nakujaproject/internship2022/Propulsion/Week 13/week 13 progress report.pdf

NAKUJA INTERNSHIP

## WEEK 13 PROGRESS REPORT

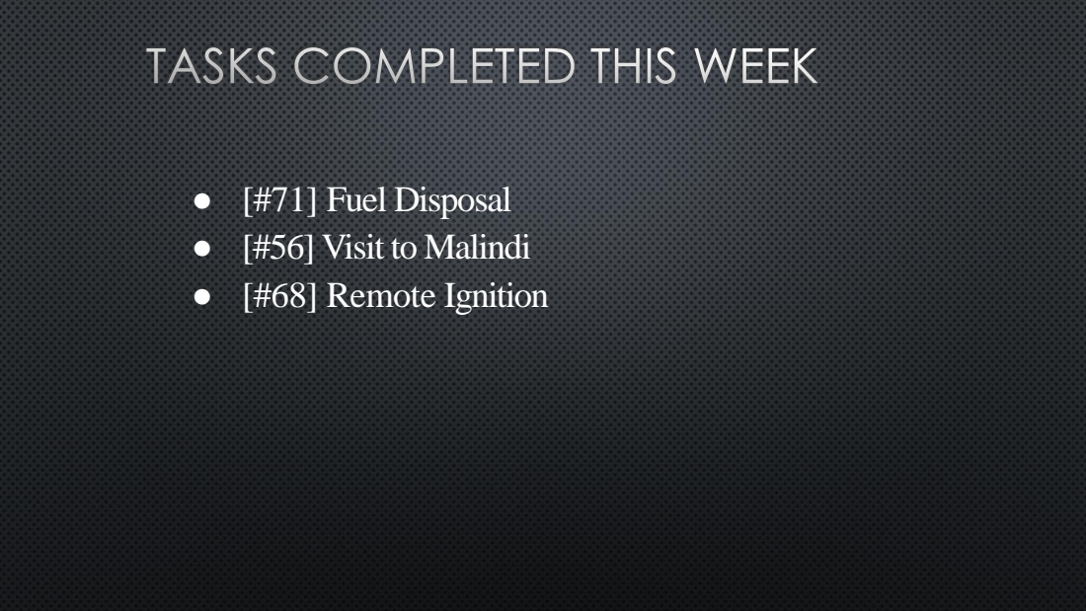
[picture p85: page 2]

● [#71] Fuel Disposal
● [#56] Visit to Malindi
● [#68] Remote Ignition

# # Safe Fuel Disposal

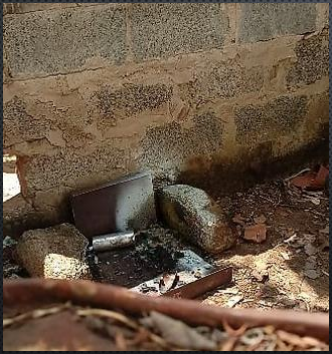
[picture p86: figure]

## The two grains of fuel

## casted on Monday had

stuck | to | the | casing

requiring safe disposal.

# # Trip to Malindi

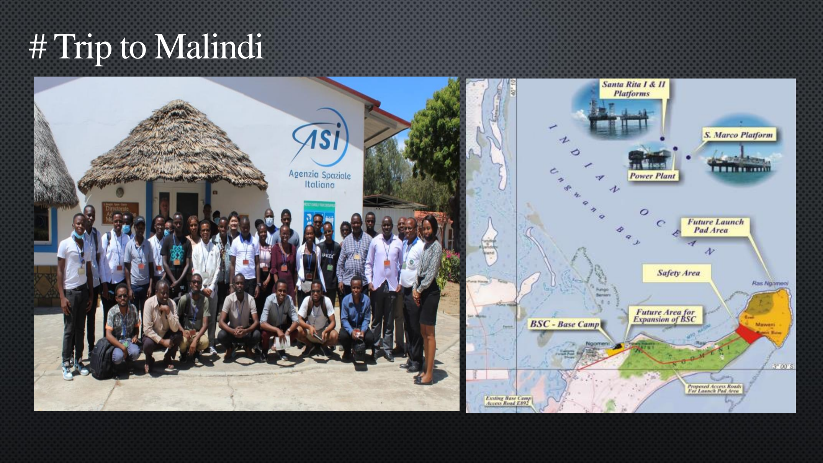
[picture p87: page 4]

## We will be using ESP32 LOLIN module to switch relay via

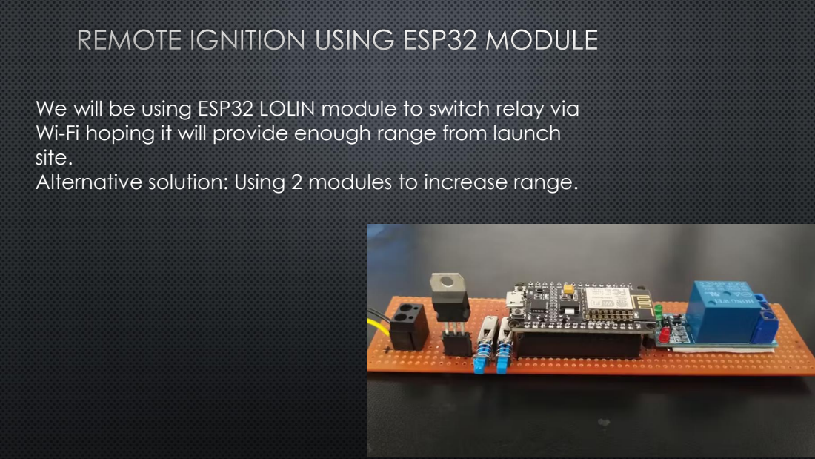
[picture p88: page 5]

Wi-Fi hoping it will provide enough range from launch
site.
Alternative solution: Using 2 modules to increase range.

TASKS THIS WEEK

## - [#108] Remote Ignition - [#36] Snap Ring Purchase - [#56] Fuel Casting for Test Flight - [#150] Test Flight

Month; Intern week; Tasks; Jan; Feb; Week 4; Fabrication of items & Fuel casting

Week 1 | Designs [Fuel, Casing, Nozzle, Bulkhead, Casting tools, Teststand]

Week 2 | Fabrication of items

Week 3 | Fuel Fabrication and test stand revamp

Week 5 | Iterative Fuel tests

Week 6 | Launch Pad design and iterative fuel tests

Week 7 | Iterative fuel testing and improvement
