nakujaproject/internship2022/Airframe/Week12/Airframeprogressreport_04_09_week.pdf

# Introduction of internship

### January 2022

Tasks done

- Fabricated the new airframe for test launch
- Tested the nichrome wire for ejection charge
- Secure skeleton for assembling the subsystems

Tasks to be done

- Nose cone adjustments and printing
- Fins fabrication
- Start assembling the skeleton ready for Friday test launch
- Print launch lug

Timeplan

April 18th - 23rd | - Test launch
| - Fabricate duplicate body tubes
April 25th - 30th | Possible launch
May 2nd - 7th | Possible launch
