nakujaproject/internship2022/Propulsion/week 11/week 11 progress report.pdf

NAKUJA INTERNSHIP

## WEEK 11 PROGRESS REPORT

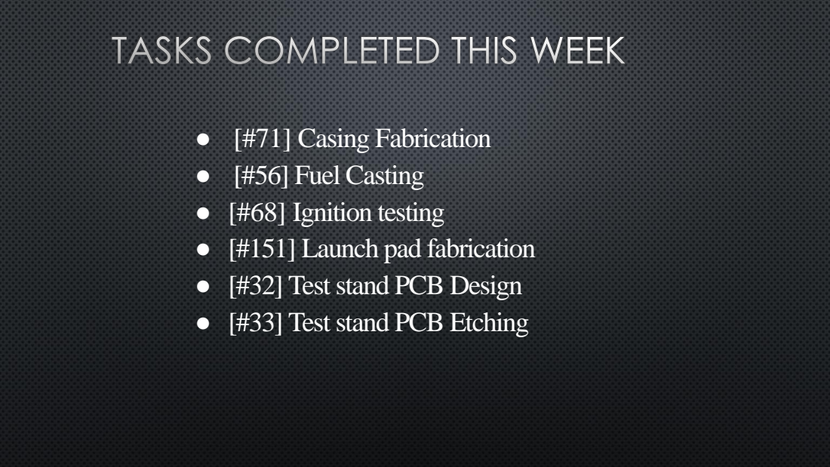
[picture p94: page 2]

● [#71] Casing Fabrication
● [#56] Fuel Casting
● [#68] Ignition testing
● [#151] Launch pad fabrication
● [#32] Teststand PCB Design
● [#33] Test stand PCB Etching

# #71 Casing fabrication

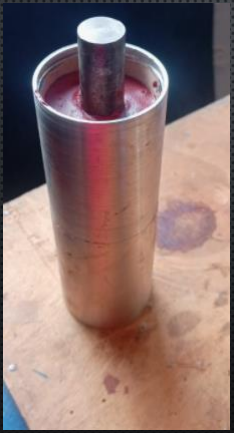
[picture p95: figure]

We | fabricated | another

## casing to be used for the

test launch on Thursday.

# Fuel Casting

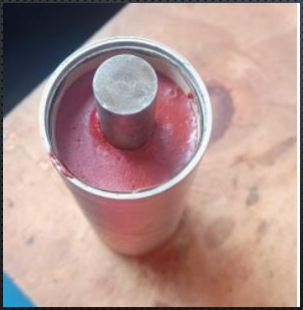
[picture p96: figure]

We prepared a single grain of fuel.

## The mixing ratio was 67:33

## potassium nitrate to sorbitol, 5g of

## iron oxide. Fuel was cast directly to

## casing. The single grain will be used

forthe testlaunch tomorrow.

# LAUNCH PAD FABRICATION

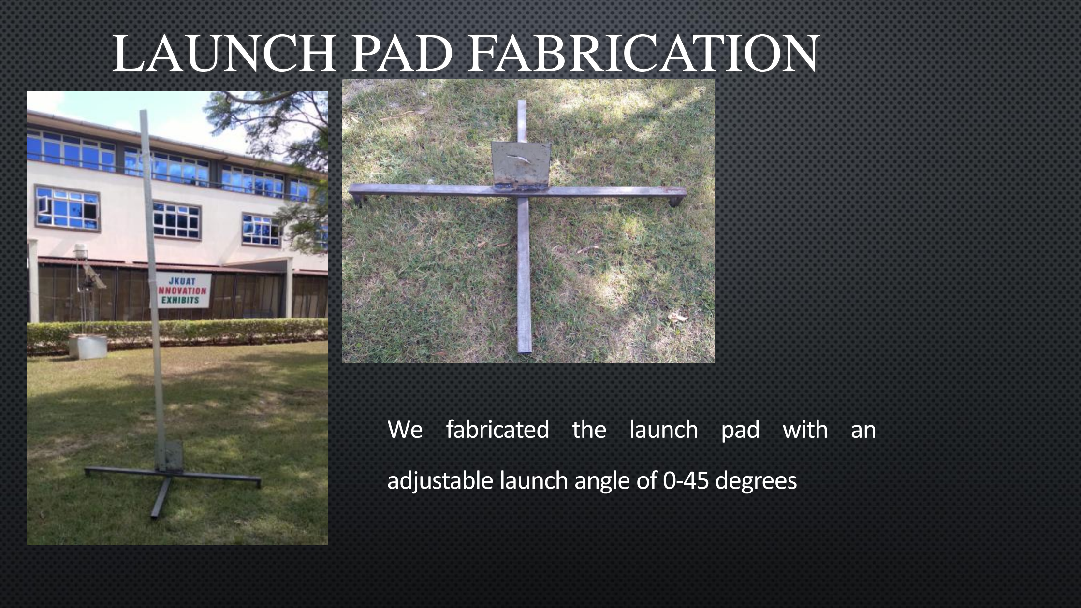
[picture p97: page 5]

## We fabricated the launch pad with an

## adjustable launch angle of 0-45 degrees

# Etched Test Stand PCB

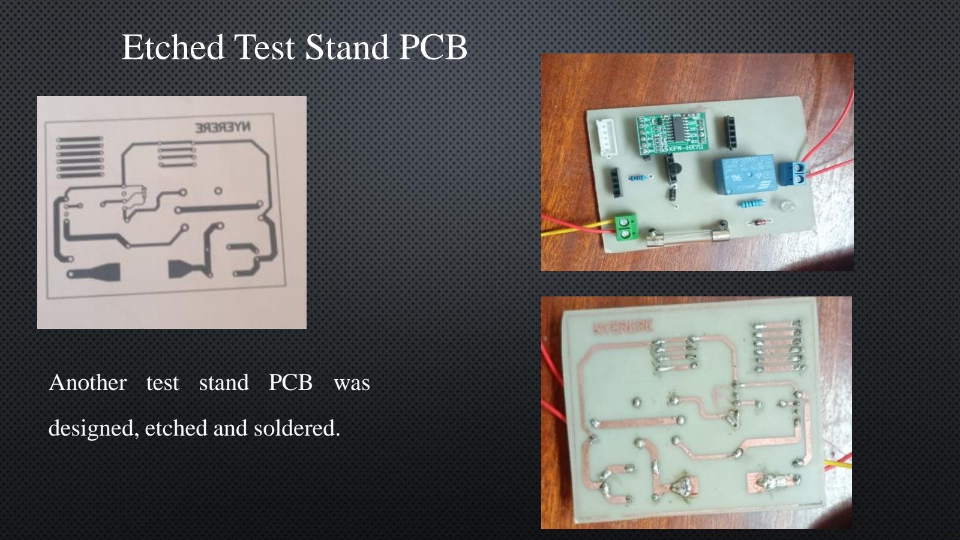
[picture p98: page 6]

### Another test stand PCB was

designed, etched and soldered.

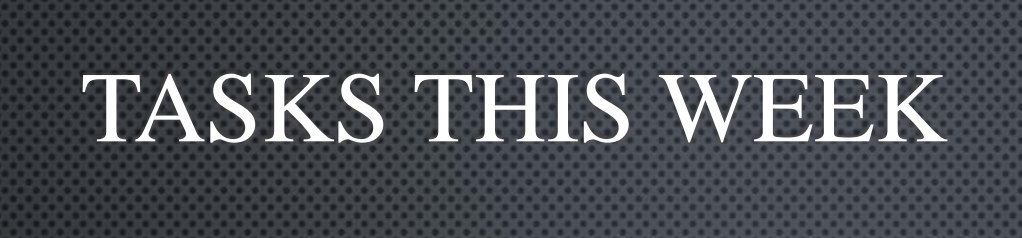
[picture p99: figure]
TASKS THIS WEEK

### - [#150] Test Flight

Month; Intern week; Tasks; Jan; Feb; Week 4; Fabrication of items & Fuel casting

Week 1 | Designs [Fuel, Casing, Nozzle, Bulkhead, Casting tools, Teststand]

Week 2 | Fabrication of items

Week 3 | Fuel Fabrication and test stand revamp

Week 5 | Iterative Fuel tests

Week 6 | Launch Pad design and iterative fuel tests

Week 7 | Iterative fuel testing and improvement
