nakujaproject/internship2022/avionics/Week6/Avionics Progress Report Week6 updated.pdf

# Nakuja Project

Week 6 Progress Report
Edwin Mwiti
Junn Hope

# Tasks this week

- [#] : Test Payload
- [#Issue 83] : Power Management
- Flight computer programming and documentation

# [#] : Test Payload

- We performed payload tests on Friday,25th Feb.
- Signal strength was also severely affected as we got RSSI values as low as -88, which was below our estimated range of -50 to -70
- The test brought to light factors we had not looked into:
- 1) Electromagnetic interference –The data received from the sensors gave negative result, a result of the interference. The drone rotors motion caused an electromagnetic field which affected the sensors operation-particularly the BMP 180.
- 2) signal interference – the RF signals from the drone interefered with the RF signals within our Wi-Fi network.

# [#] : Test Payload

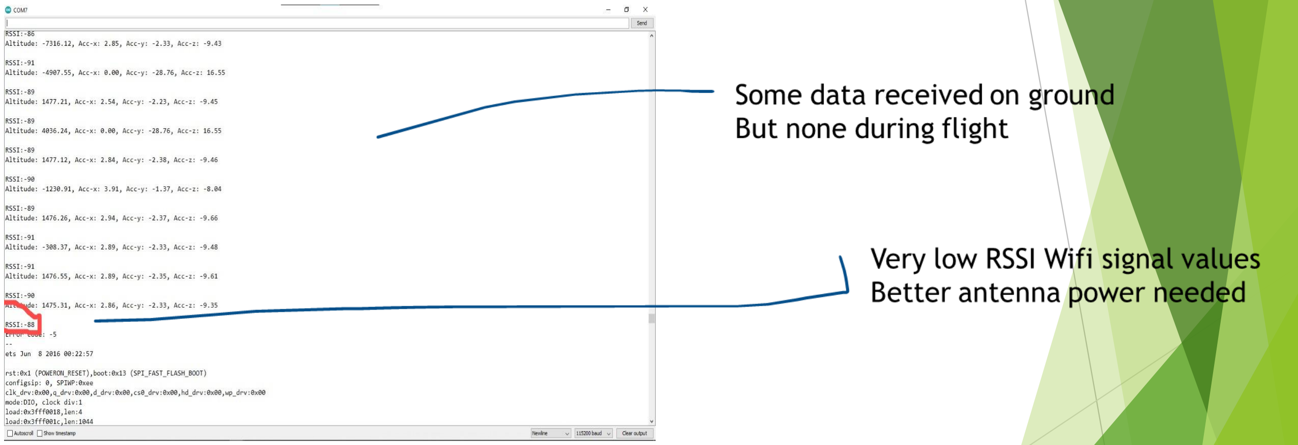
[picture p161: figure]

## Flight computer programming and documentation

- Ongoing programming of flight computer
- Restructuring code as a state machine
- Every interval is a state. E.g
- This will help in scaling the software for future versions
- Observation: need to have a means of restarting the flight computer remotely

# [#Issue 83] : Power Management

- The design of the power distribution board is done and is currently under review

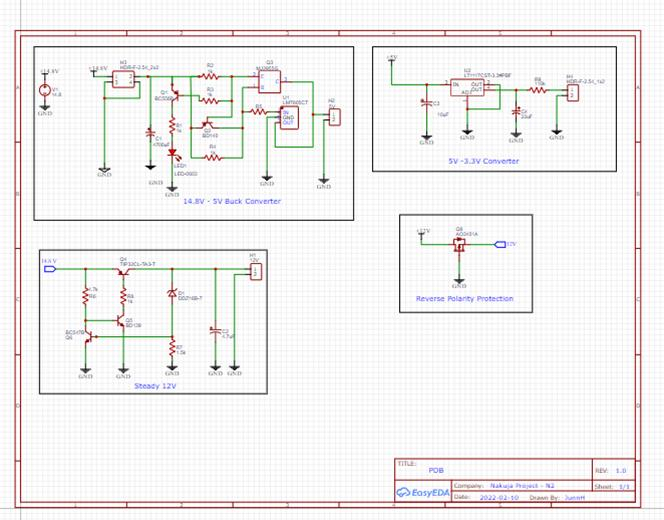
[picture p162: figure]

# Tasks this week

- [#Issue 26] : Improve on Kalman filter performance
- [#Issue 103] : Build Wi-Fi Amplifier
- [#Issue 34] : Programming the Flight Computer
- [#Issue 18] : Launch pad design
