nakujaproject/internship2022/Propulsion/Week 5 (10th - 16th)/Valerian Nyerere Progress Report.pdf

# Internship 2022

# Progress report format for team meeting

Name: NYERERE VALERIAN
09/02/2/2022 - 15/02/2022

## Tasks completed last week

- [#56] Fuel fabrication (Wednesday)
- [#71] Casing fabrication (Thursday)
- [#72] Crimson powder development.(Friday)
- [#32] Design of the Test-Stand PCB redo (Monday)
- [#88] Crimson powder ejection test. (Tuesday)

## Fuel Fabrication

We had to fabricate more fuel following the right procedure and ratio.

We used 65% potassium nitrate and 35% sorbitol.

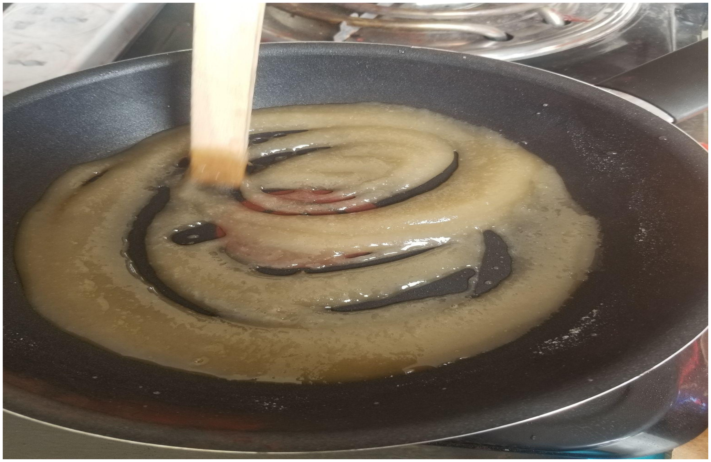
[picture p163: figure]

## Crimson powder test

Tested the crimson powder explosion rate.

Found out the more dry it is, the more efficient it works.

## Crimson powder development

Developed more crimson powder taking into consideration the observations made in the first ejection test.

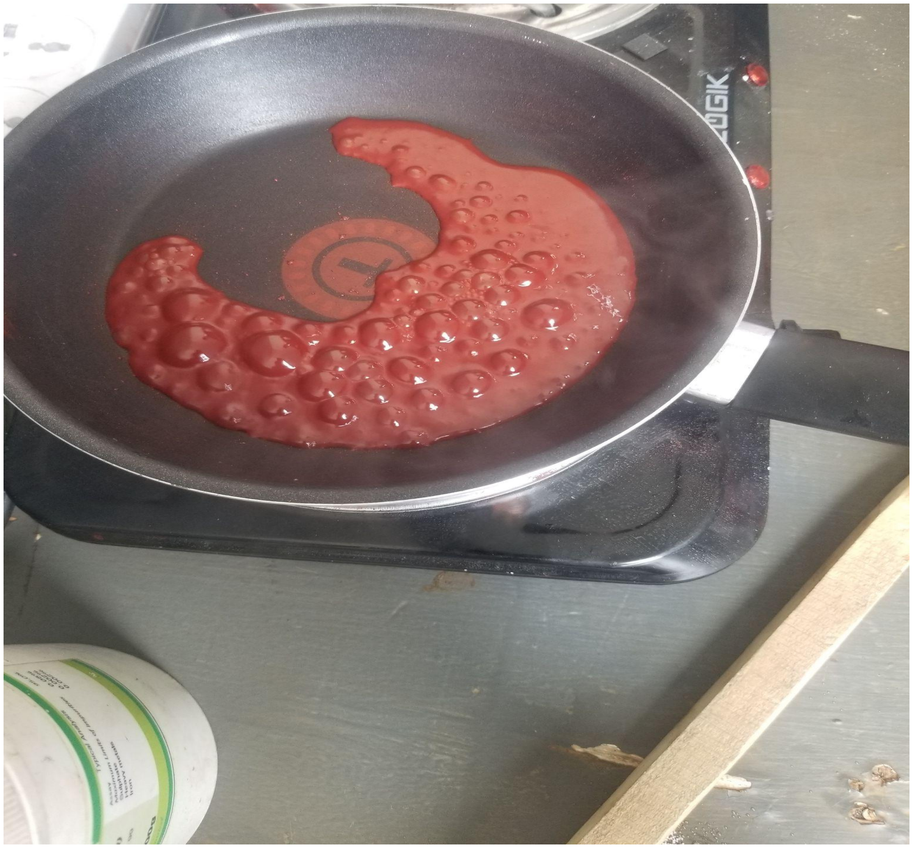
[picture p164: figure]

## Design of the Test-stand PCB

Redesigned the Test-stand PCB.

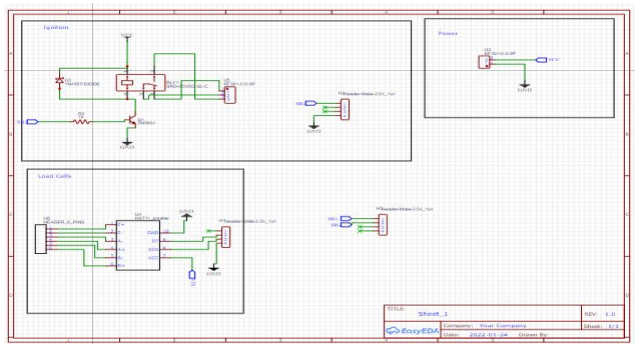
[picture p165: figure]

Still in progress.

## Tasks in this week

- [#85] Preparation of potassium perchlorate.
- [#33] Test stand PCB etching.
- [#19] Static firing tests.

## Timeline

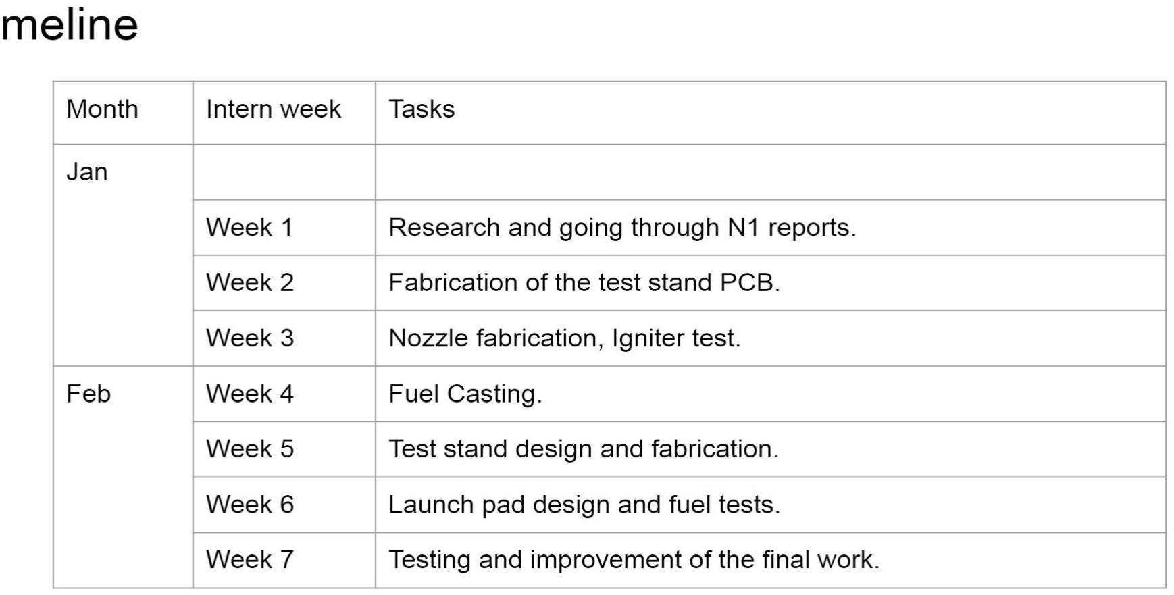
[picture p166: page 8]

Month | Intern week | Tasks

Jan

Week 1

Week 2

Week 3

Feb | Week 4

Week 5

Week 6

Week 7
