nakujaproject/internship2022/Propulsion/Week 6 (17th - 23rd)/Valerian Progress Report.pdf

## Internship 2022

## Progress report format for team meeting

Name: NYERERE VALERIAN KWAMBOKA 16/02/2022- 22/02/2022

Tasks completed last week

- [#32] Test stand PCB design
- [#33] PCB Etching.
- [#68] Ignition Testing.
- [#19] Iterative static firing test. (First)

PCB DESIGN AND ETCHING(Failed)

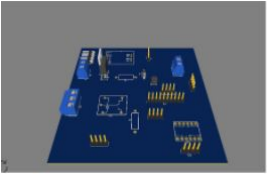
[picture p167: figure]

The first three designs failed. This is the current design that is being etched at the moment.

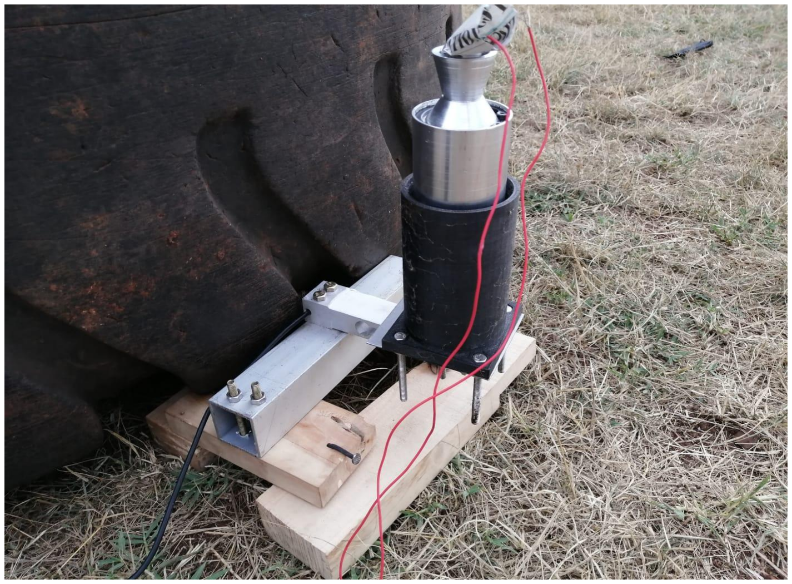
[picture p168: figure]

STATIC FIRING

The setup of the test stand.

STATIC TEST FIRING VIDEO

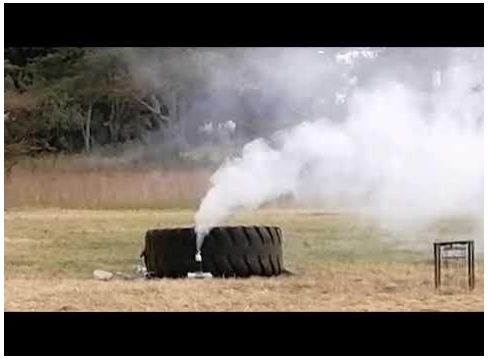
[picture p169: figure]

OBSERVATIONS.

- The igniter took a few seconds before igniting opposed to the immediate response we expected. That was after several tries.
- The fuel took close to one minute before it fully burnt out. According to the simulations, the fuel should take 2 seconds to burn out.
- No data was collected from the Raspberry Pi.

Tasks in this week

- [#85] Preparation of Potassium Perchlorate.
- [#56] Fuel casting.
- [#32] Test stand PCB design
- [#33] PCB Etching.
- [#68] Preparation and Ignition Testing.
- [#71] Casing fabrication (Finalising).

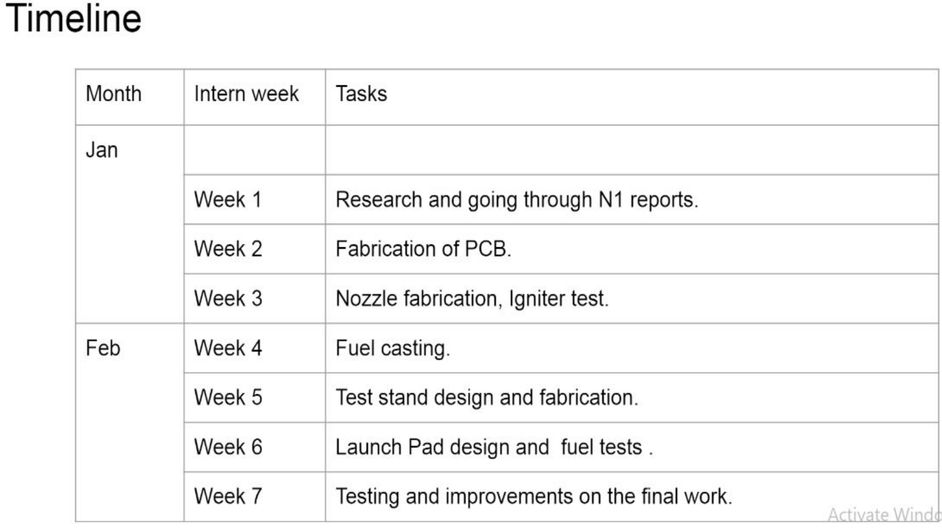
[picture p170: page 8]

Timeline

Month | Intern week | Tasks

Jan

Week 1

Week 2

Week 3

Feb | Week 4

Week 5

Week 6

Week 7
