nakujaproject/internship2022/Propulsion/Week 4 (3rd - 9th)/Valerian Nyerere. Progress Report.pdf

# Internship 2022

# Progress report format for team meeting

## Name: NYERERE VALERIAN

02/02/2022 - 09/02/2022

# Tasks completed last week

## - [#56] Fuel casting (Wednesday) - [#22] Static fire safety orientation (Thursday) - [#11] Casting tool fabrication (Friday) - [#72] Crimson powder development (Monday - Tuesday)

# Fuel casting

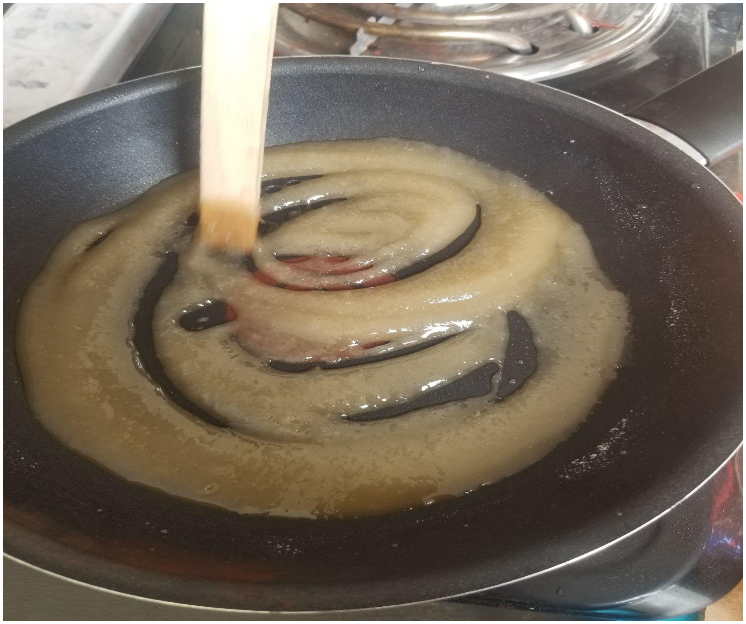
[picture p234: figure]

Heating a mixture of potassium nitrate and sorbitol to make the fuel. In the ratio 65: 35
respectively.

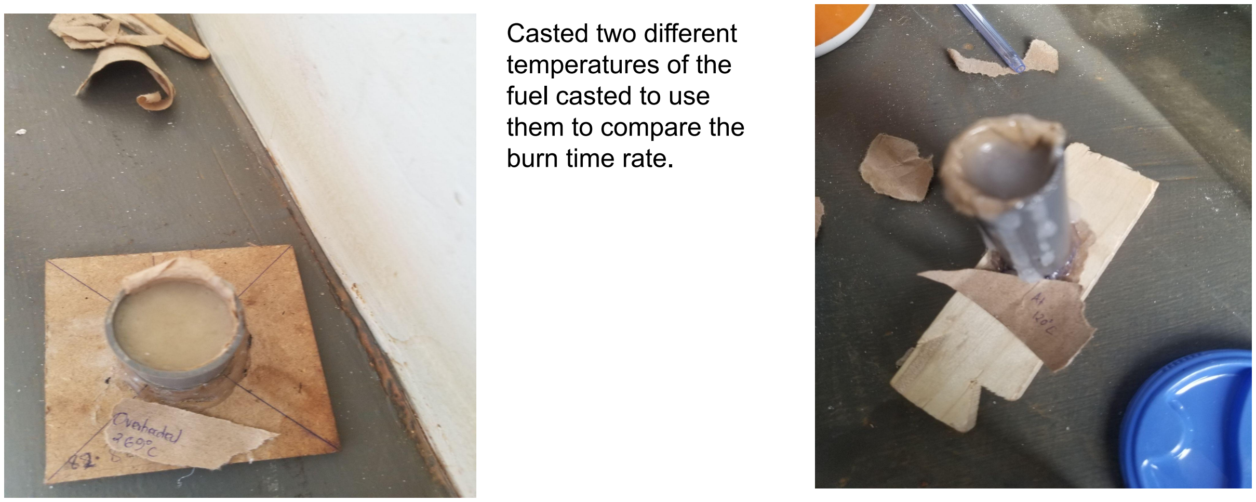
[picture p235: page 4]

Casted two different
temperatures of the
fuel casted to use
them to compare the
burn time rate.

# Casting tools fabrication

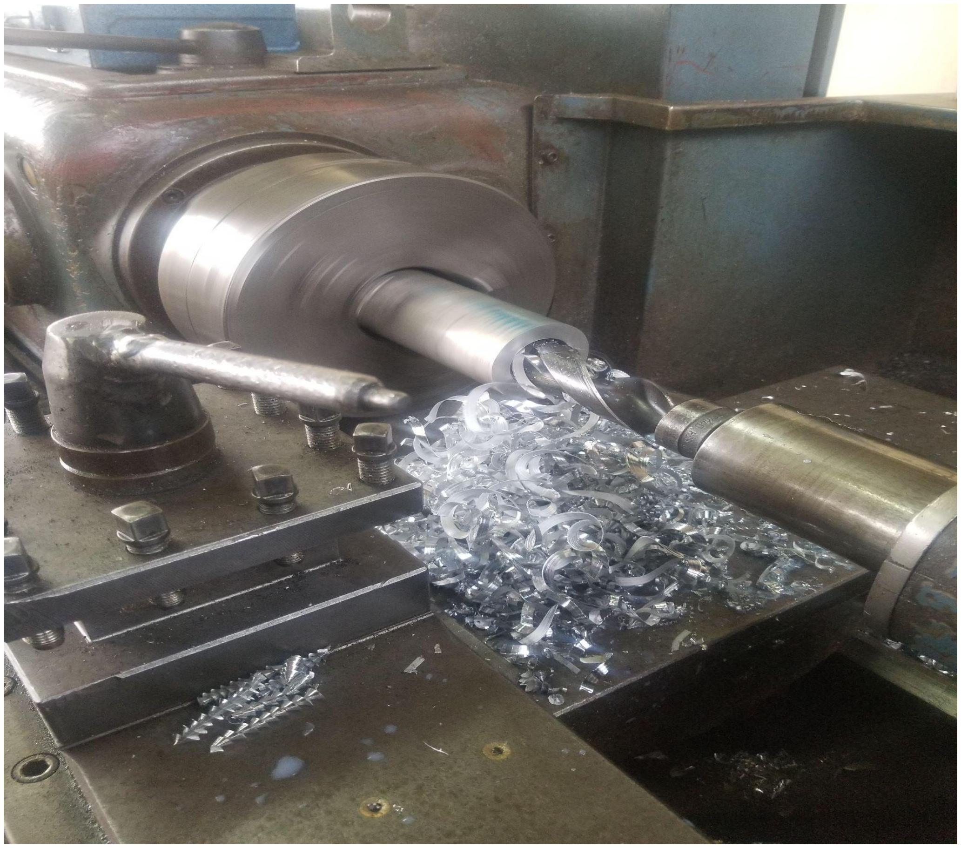
[picture p236: figure]

# Crimson Powder Development

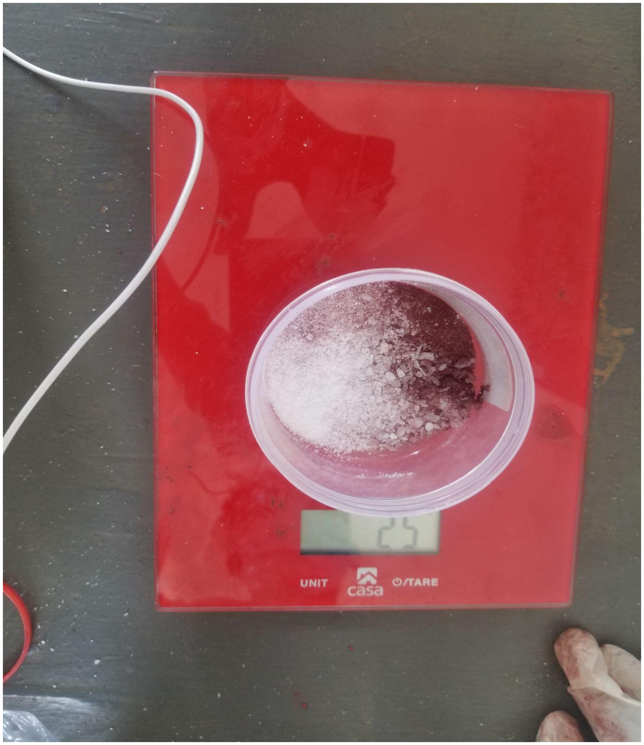
[picture p237: figure]

A mixture of potassium nitrate, iron oxide and ascorbic acid to make the ejector.

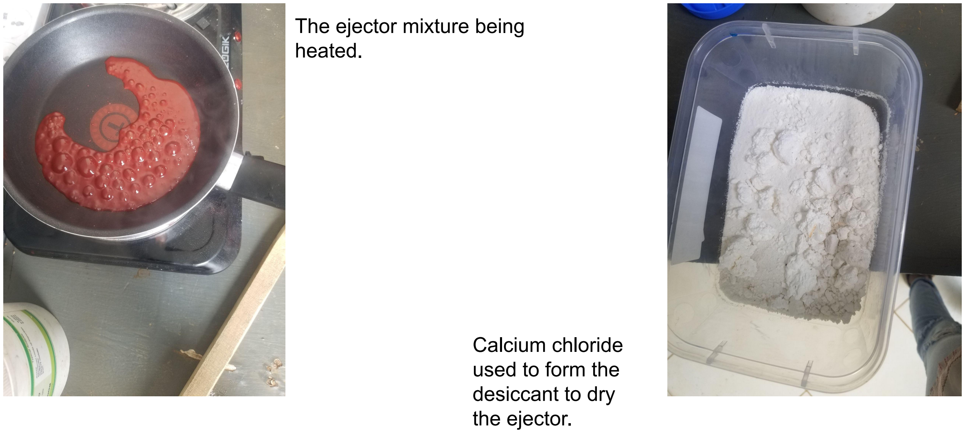
[picture p238: page 7]

The ejector mixture being
heated.

Calcium chloride
used to form the
desiccant to dry
the ejector.

# Tasks in this week

## - [#69] KNPSB Trials - [#71] Casing fabrication - [#56] Fuel fabrication - #73] KNSB Burn time tests

# Timeline

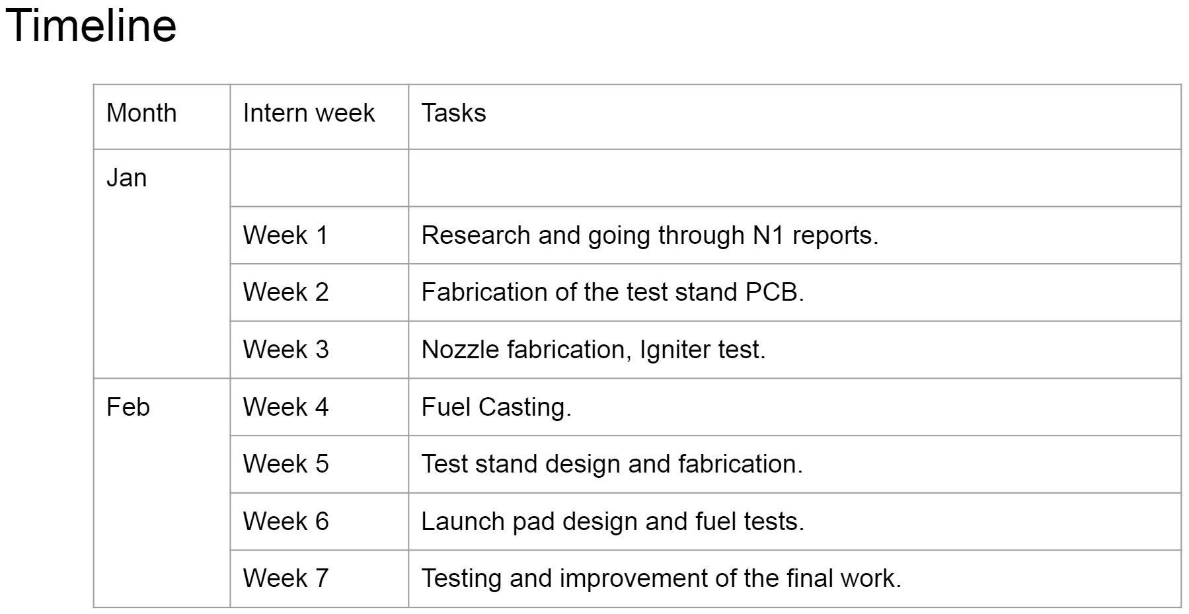
[picture p239: page 9]

Month | Intern week | Tasks

Jan

Week 1

Week 2

Week 3

Feb | Week 4

Week 5

Week 6

Week 7
