nakujaproject/internship2022/avionics/Week 1/Nakuja internship Progress report week1.pdf

# Nakuja Internship

# Avionics Progress report

# Edwin Mwiti Junn Hope

# Tasks completed last week

## - [#Issue 4] : Getting acquainted with Avionics and Telemetry resources

## - Onboarding and task planning

## - Flight computer 2 review

# COMMUNICATION CHANNELS

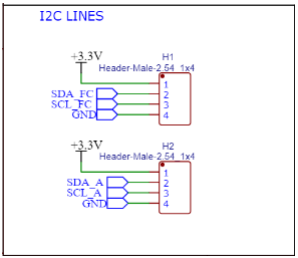
[picture p241: figure]

## - I2C Communication - Avionics board - Flight control board

Flight
control
board

Telemetr
y

Avionics
board

Ground station

Lora/Wifi

i2c

# STORAGE

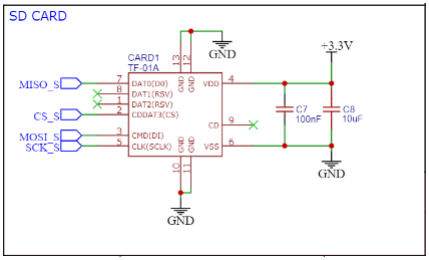
[picture p242: figure]

## - SD CARD MODULE

## Post flight analysis data

## -velocity

## -acceleration

## -gyroscope(orientation)

## -altitude data

# Flight recovery

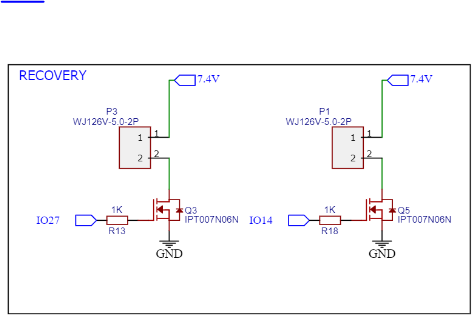
[picture p243: figure]

## Flight recovery system:

## - Parachute deployment

## esp32 ~ 140mA

## mosfet ~ 2A

# Motion Tracking(MPU6050)

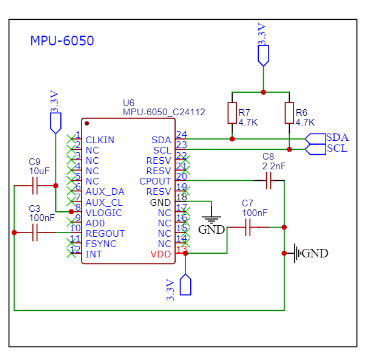
[picture p244: figure]

## - Flight motion tracking:

## Gyroscope

## Accelerometer

# Flight Navigation

## GPS System

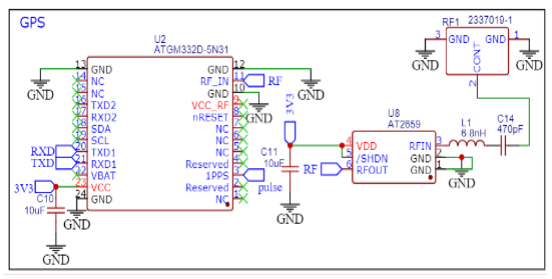
[picture p245: figure]

## - Transmit real-time location data to ground station - For recovery

# Tasks in this week

## - [#Issue 1] : Research on data transmission (lora vs wifi) parameters: 1km > upload speed 272.16 kbps - [#Issue 2] : Research on ground station parameters: 1km > download speed 1000 kbps - [#Issue 3] : Research on ground station dashboard-Grafana - [#Issue 30]: Research on camera module

## Timeline

Month | Intern week | Tasks
| | Getting acquainted with avionics and telemetry resources
| Week 2 | Research on ground station & ground station dashboard Research on camera module Research on Data transmission
| Week 3 | Avionics bay design Launch pad design
| | Improve Kalman filter performance
| Week 5 | Program Avionics and Telemetry boards
| Week 6 | Test the boards
| Week 7 | Testing and launch of N2
Jan | Week 1 | Onboarding
Feb | Week 4 | Research on apogee detection logic
