nakujaproject/internship2022/Flight_Controls/Week 3 (26th - 2nd)/Week3 (upload)progress report.pdf

# Nakuja Internship 2022 Week 3 Progress report format for team meeting

## Name:FLIGHT CONTROL

# Tasks completed last week

- [#29] Soldering of SD card on PCB
- [#24] Design of the reaction wheel

[#29] Soldering of SD card on PCB

Soldering of PCB involved microcontroller pin out identification and connecting the respective pins to the SD card pins

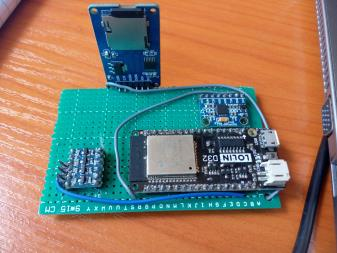
[picture p255: figure]

[#24] Design of the reaction wheel

This was done with the help of simulink(in progress)

# Tasks in this week

- [#24] Design of the reaction wheel(completion)
- [#29] Logging data on SD Card
- [#25]Testing reaction wheel on test bench with current firmware
- [#27]Design mounting case

[#24] Design of the reaction wheel(completion)

This involves design optimization of the CAD model of reaction wheel and fabrication [#29] Logging data on SD Card&[#25]Testing reaction wheel on test bench with current firmware
The two tasks will be done concurrently. The code for this is in progress
[#27]Design mounting case

Onset of the design

## Timeline

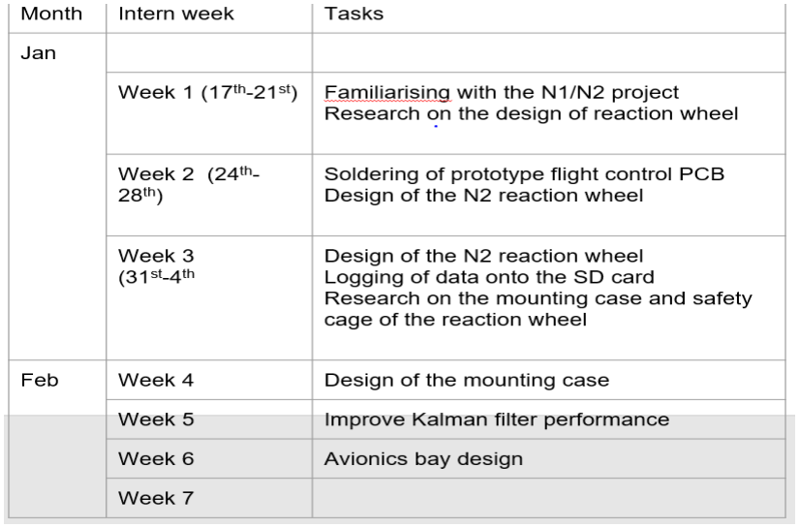
[picture p256: figure]
