nakujaproject/internship2022/Propulsion/Week 3 (26th - 2nd)/Maureen's PROGRESS REPORT.pdf

# Internship 2022

# Wk 3 Progress report

### Name: Gichia Maureen

## Tasks completed last week

[#53]Bulkhead fabrication

[#63]Research on teststand design including use of load cells and the configuration

[#67]Research on N2 motor fuel and work plan development(ongoing)

[#55] Test of new loadcell configuration

[#56] Motor fuel casting1

### [#53]Bulkhead fabrication

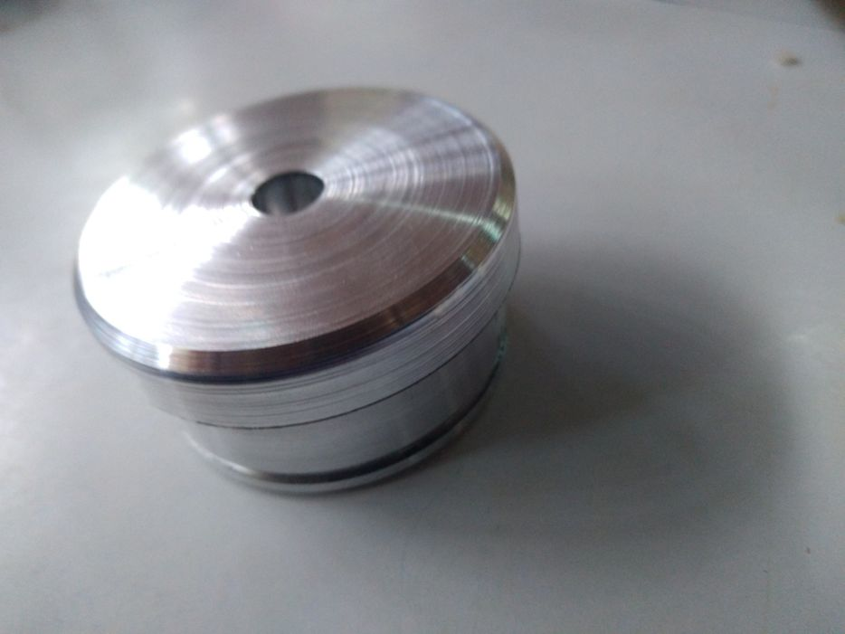
[picture p260: figure]

### [#56] Motor fuel casting1

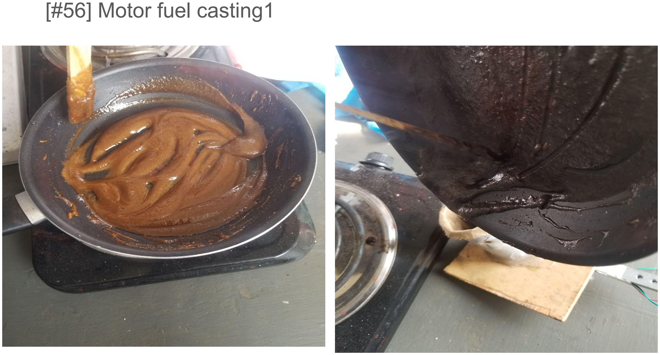
[picture p261: page 4]

## Tasks in this week

●[#52] Nozzle fabrication

- [#21] Research on modification of KNSB fuel
- [#11] Casting tools fabrication
- [#56] Fuel Casting
- [#64] Test stand fabrication
- [#19] Iterative static firing tests
- [#22] Static fire safety orientation

## Timeline

Month | Intern week | Tasks

Jan

Week 1

Week 2

Week 3

Feb | Week 4

Week 5

Week 6

Week 7
