nakujaproject/internship2022/Airframe/Week 1 progress/Airframe.pdf

# Internship 2022

# Progress report format for team meeting

Name: Mark and Vivian

## Tasks completed last week

- [#Github issue number #37]

Describe the completed task with the GitHub issue number

This was the material selection and analysis

## Tasks in this week

- [#Github issue number #38]

This is the design and simulation of the rocket using openrockets.

## Timeline

Month | Intern week | Tasks

Jan

Week 1 | Material selection and analysis
Week 2 | Design and simulation
Week 3 | Fluid dynamics
Feb | Week 4 | Simulation and rocket recovery
Week 5 | Assembly
Week 6 | Assembly
Week 7 | Take-off?
