nakujaproject/internship2022/Propulsion/Week 2(20th - 26th)/Week 2 progress.pdf

# NAKUJA PROJECT INTERNSHIP

# PROGRESS REPORT

# WEEK 2 (20TH JANUARY - 26TH JANUARY)

## Tasks achieved:

## - Purchase of items. - Issue #36

## - Bulkhead design. - Issue #35

## - Casing design. - Issue #6

## - Design and 3D printing of electronics hub. - Issue #16 & 9

## - PCB Design & Etching. - Issue #33 & 32


# 3D PRINTED ELECTRONICS BAY

# TEST STAND PCB


# NOZZLE DESIGN


# NOZZLE FABRICATION


# BULKHEAD DESIGN


# CASING DESIGN


# CASTING TOOLS DESIGN


# MOTOR


# SIMULATION DATA

501 Ns

## Core dia - 17 mm

## Nozzle throat - 12 mm

## Casing thickness - 2 mm

## Design Pressure - 3 Mpa


# Tasks in progress

- Nozzle fabrication.

# - PCB fabrication - (Soldering)

- Design of casting tools.
- Purchase of items.

# Tasks to be done

- Fabrication of Casing and bulkhead.

## - Nozzle fabrication (Finalising)

## - Casting tools fabrication

- Test stand optimization.
- Cast fuel.

# TIMELINE

MONTH | WEEK | ACTIVITY
JAN | 1 | Designs [Casing, Nozzle, Bulkhead, Casting tools, test stand]
| 2 | Fabrication [Casing, Nozzle, Casting tools]
FEB | 3 | Casting of fuel and Test Stand revamp
| 4 | Iterative static firing tests
| 5 | Iterative static fires and fuel improvement
| 6 | Launch Pad design and Fabrication
MAR | 7 | Iterative Static Fires
| 8 | Launch
