nakujaproject/internship2022/Propulsion/Week 1(17th - 19th)/Week 1 progress.pdf

# NAKUJ A PROJECT INTERNSHIP

## PROGRESS REPORT

# WEEK 1 (17 TH JANUARY - 19 TH JANUARY)

Tasks achieved:
- Onboarding and work / tasks planning
- Set up github repository and arrange all relevant info
- Test stand review
- Creation of BOM and first purchase of items.

# Tasks in progress

- Purchase of items
- Bulkhead design
- Design of electronics hub

# Electronics Hub


# Tasks to be done

- 3D printing of electronics hub
- Fabrication of Nozzle, Casing and bulkhead
- Test stand optimization
- Cast fuel
