nakujaproject/internship2022/Flight_Controls/Week 8/NAKUJA PROJECT WEEK 8 PROGRESS REPORT.pdf

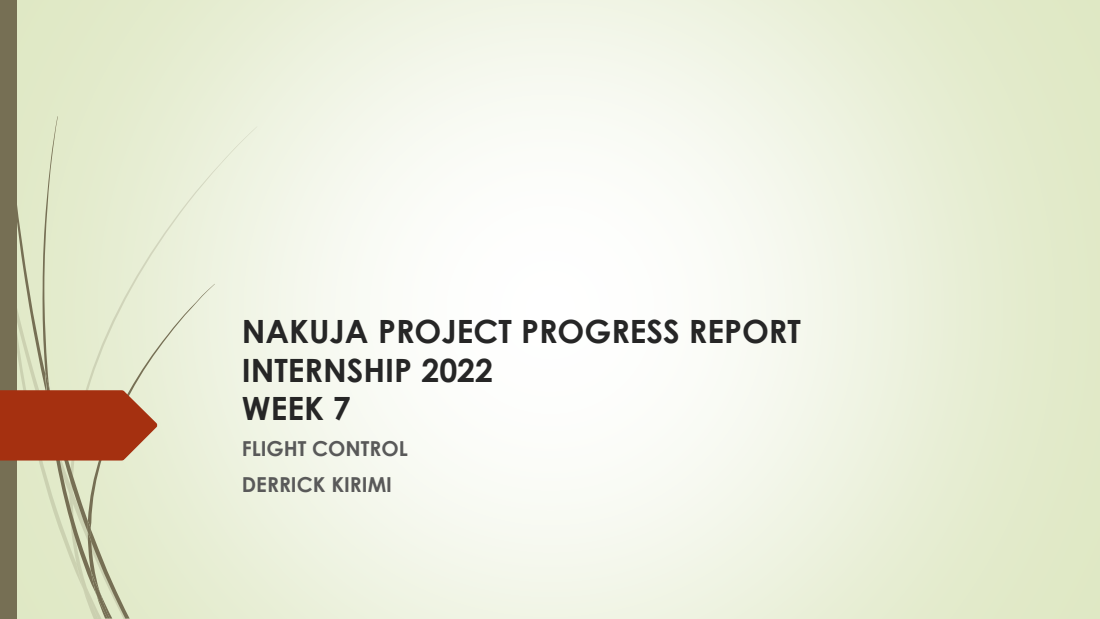
[picture p312: page 1]
FLIGHT CONTROL; DERRICK KIRIMI

NAKUJA PROJECT PROGRESS REPORT
INTERNSHIP 2022
WEEK 7

# TASKS LAST WEEK

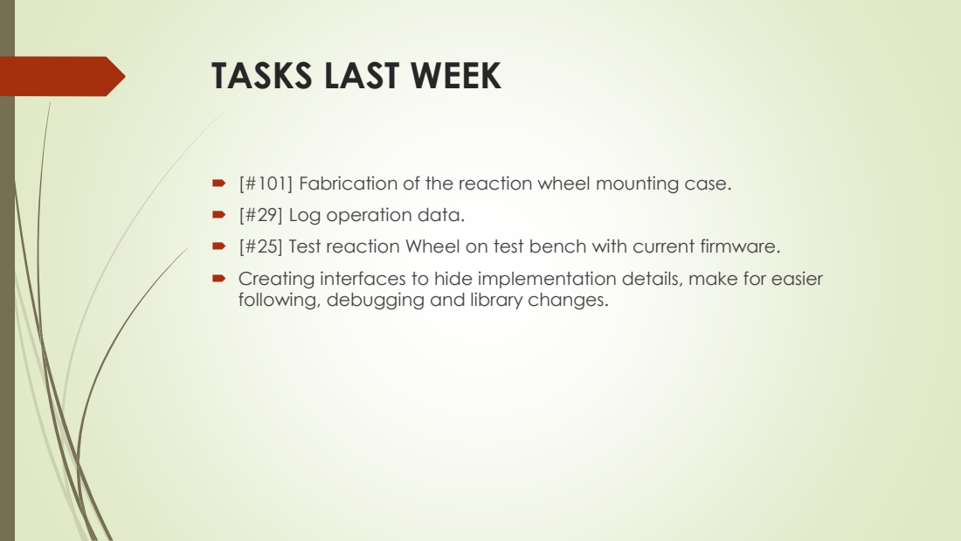
[picture p313: page 2]

[#101] Fabrication of the reaction wheel mounting case.
[#29] Log operation data.
[#25] Test reaction Wheel on test bench with current firmware.
Creating interfaces to hide implementation details, make for easier
following, debugging and library changes.

# [#101] Fabrication of the reaction wheel

mounting case.

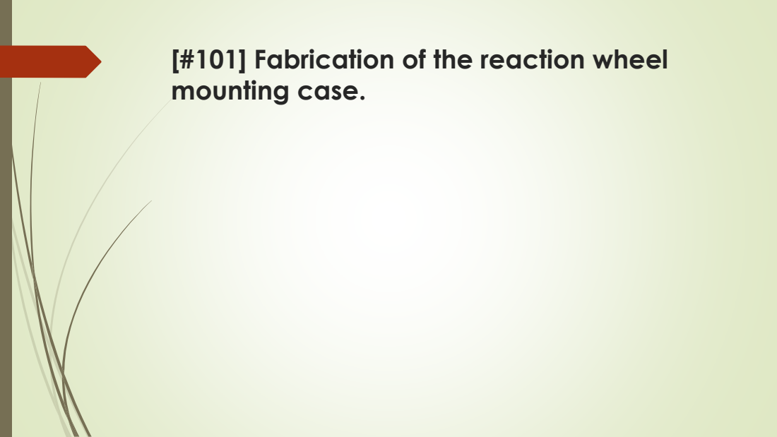
[picture p314: page 3]

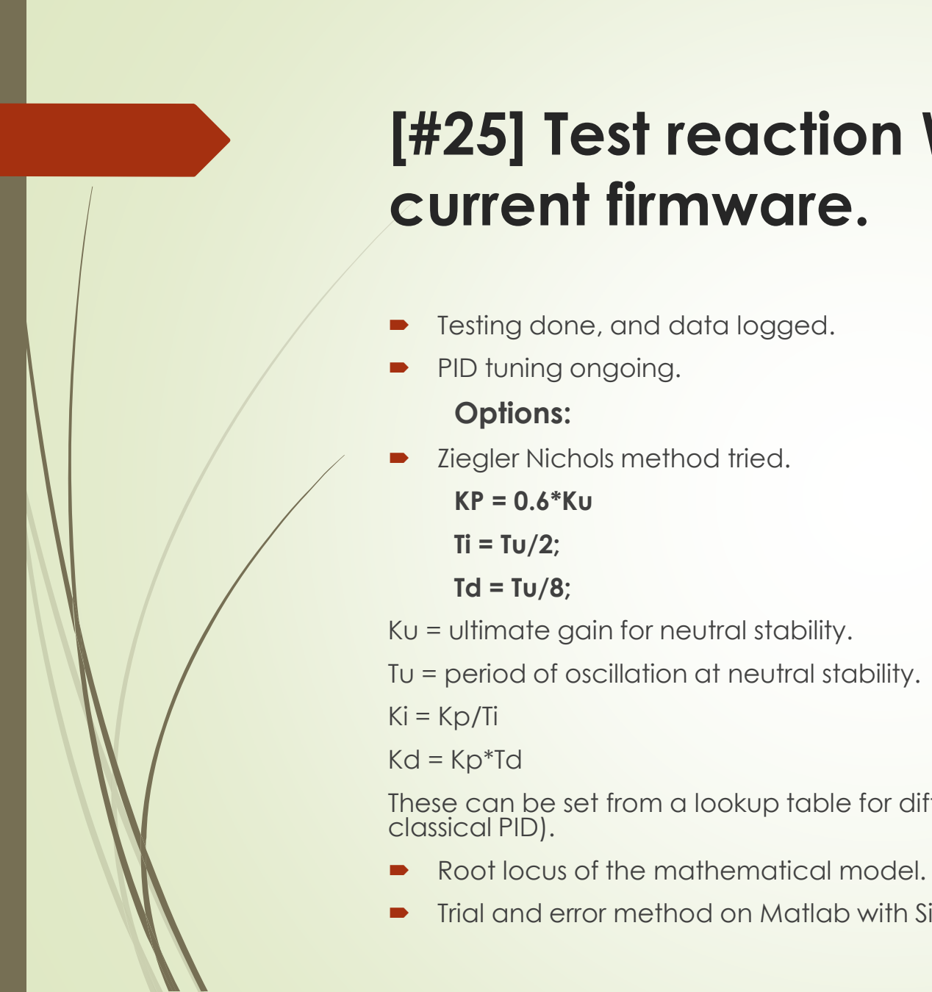
[picture p315: figure]
current firmware.; Testing done, and data logged.; PID tuning ongoing.; Options:; Ziegler Nichols method tried.; classical PID).; Root locus of the mathematical model.

# [#25] Test reaction Wheel on test bench with

Ku = ultimate gain for neutral stability.
Tu = period of oscillation at neutral stability.

These can be set from a lookup table for different controller requirements (No overshoot, PD, PI,

- Trial and error method on Matlab with Simulink blocks.

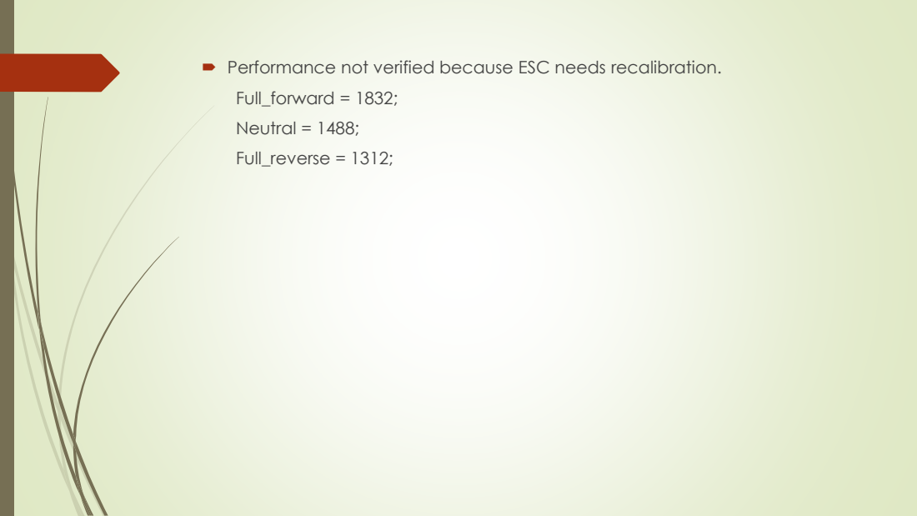
[picture p316: page 5]

Performance not verified because ESC needs recalibration.
Full_forward = 1832;
Neutral = 1488;
Full_reverse = 1312;

[#29] Log operation data.

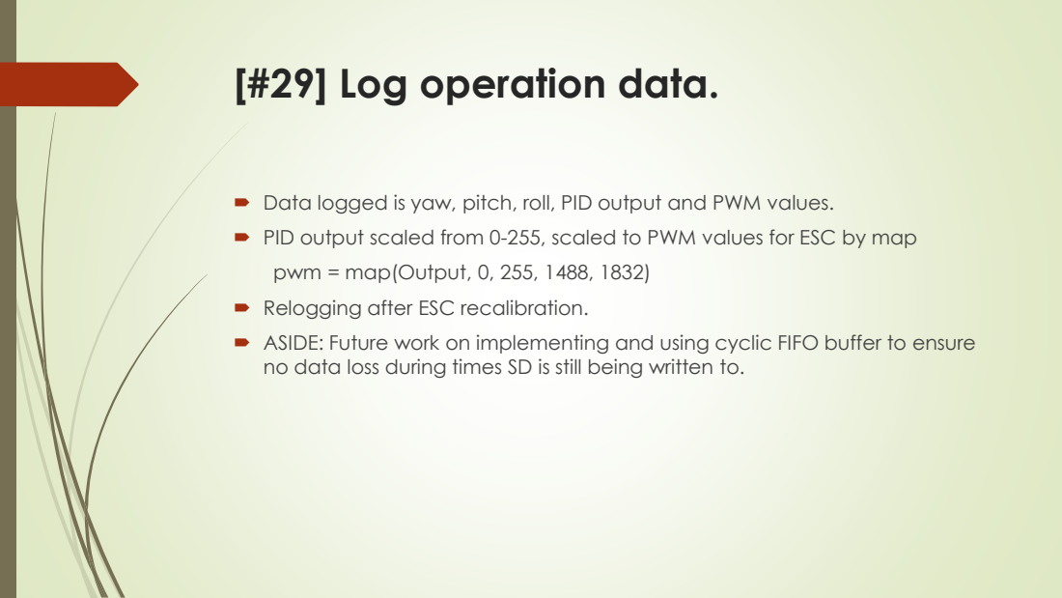
[picture p317: page 6]

Data logged is yaw, pitch, roll, PID output and PWM values.
PID output scaled from 0-255, scaled to PWM values for ESC by map
pwm = map(Output, 0, 255, 1488, 1832)
Relogging after ESC recalibration.
ASIDE: Future work on implementing and using cyclic FIFO buffer to ensure
no data loss during times SD is still being written to.

# TASKS THIS WEEK

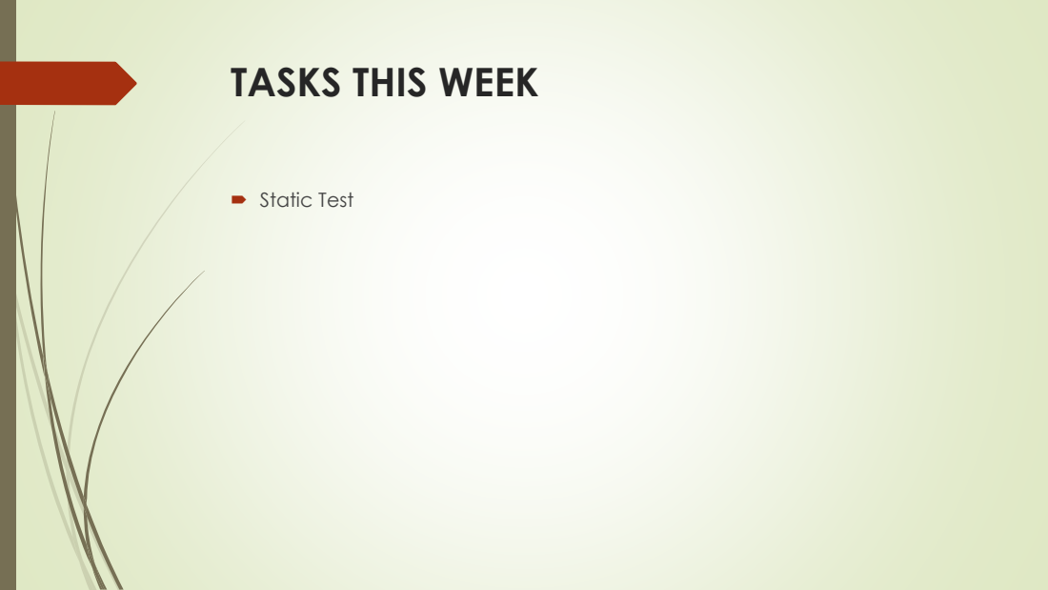
[picture p318: page 7]
Static Test

# TIMELINE Timeline

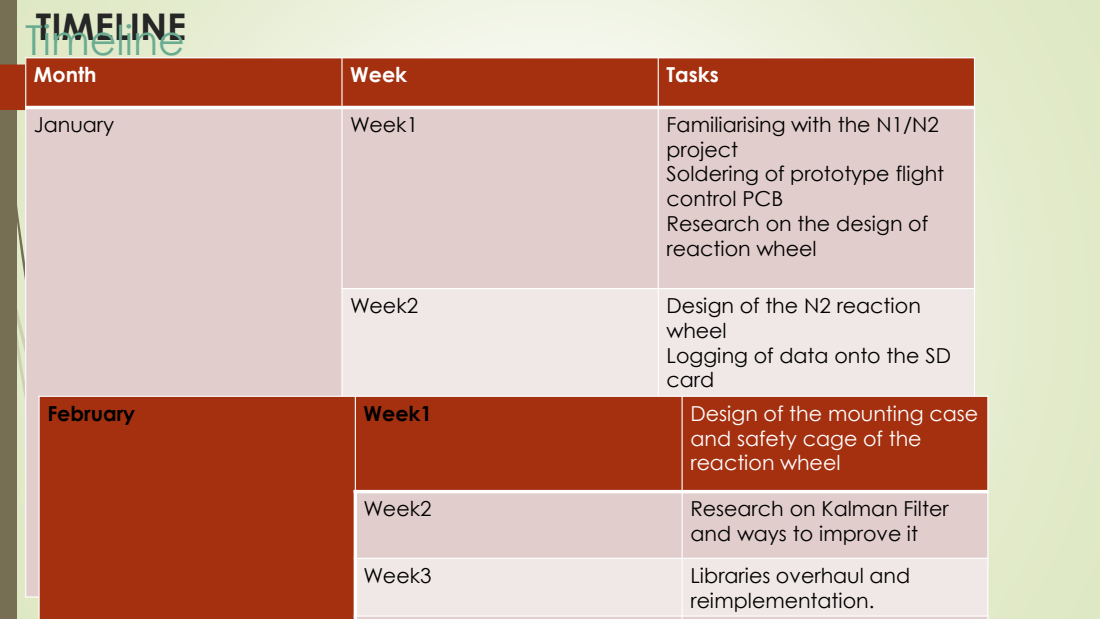
[picture p319: page 8]
January; Week1; Familiarising with the N1/N2; Week3; Week4; February; Design of the mounting case; Week2; Research on Kalman Filter; Libraries overhaul and; reimplementation

Month | Week | Tasks

project Soldering of prototype flight control PCB Research on the design of reaction wheel

Week2 | Design of the N2 reaction wheel Logging of data onto the SD card

Research on the mounting case and safety cage of the reaction wheel | and safety cage of the reaction wheel

and ways to improve it
